TiagoJustino/surfcube/images/image00.jpg

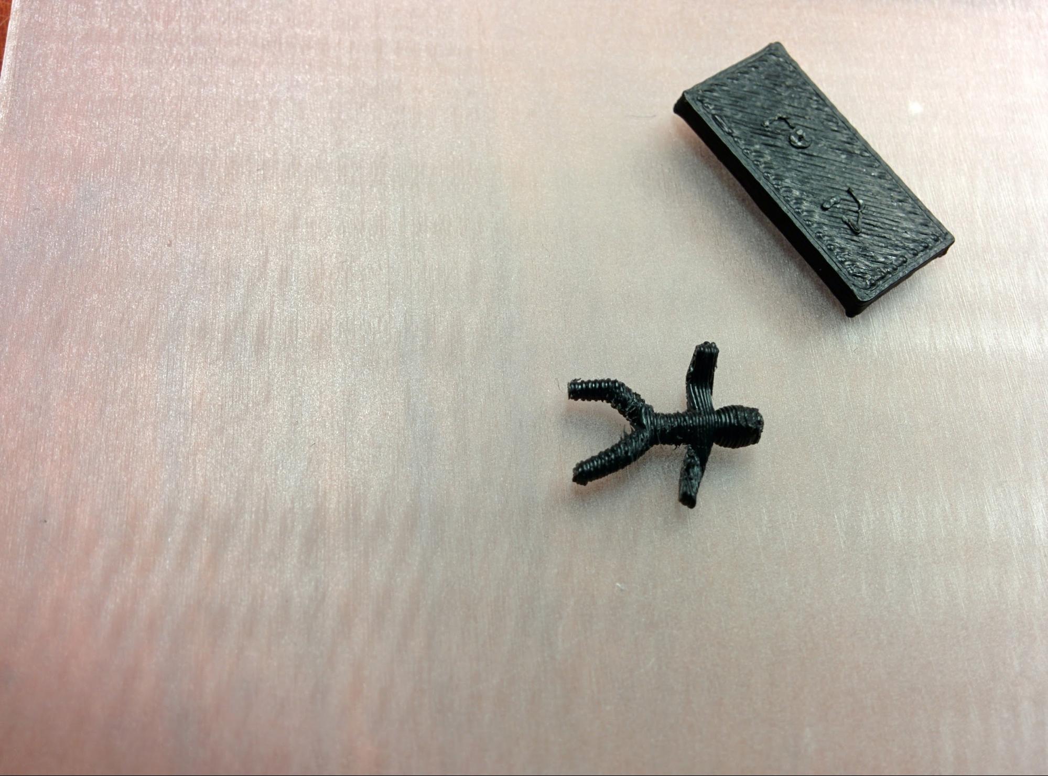
images/image00.jpg
