TiagoJustino/surfcube/sketches/IMG_20151026_231950.jpg

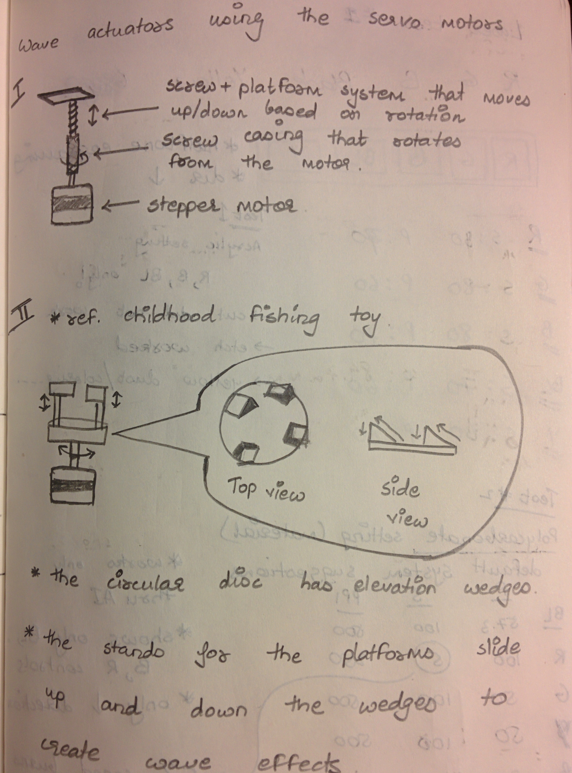
sketches/IMG_20151026_231950.jpg
