TiagoJustino/surfcube/sketches/IMG_20151026_232008.jpg

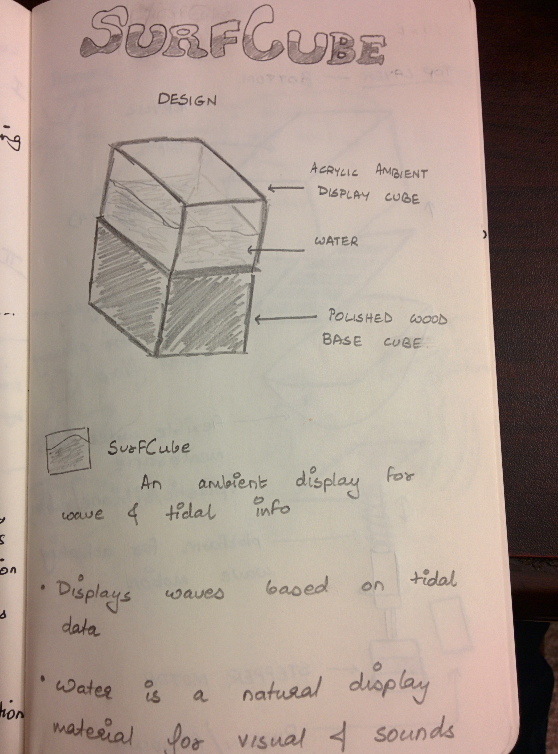
sketches/IMG_20151026_232008.jpg
