TiagoJustino/surfcube/sketches/IMG_20151026_232026.jpg

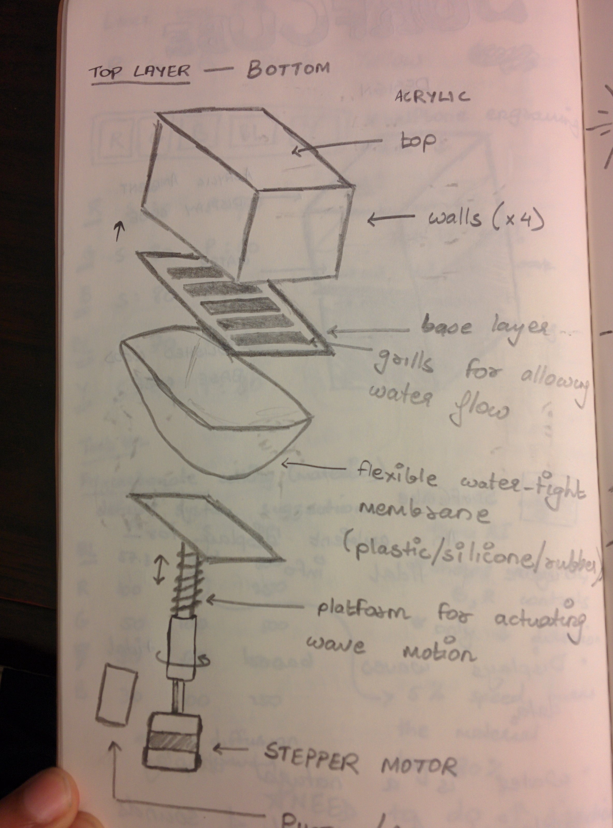
sketches/IMG_20151026_232026.jpg
