TiagoJustino/surfcube/sketches/IMG_20151026_232033.jpg

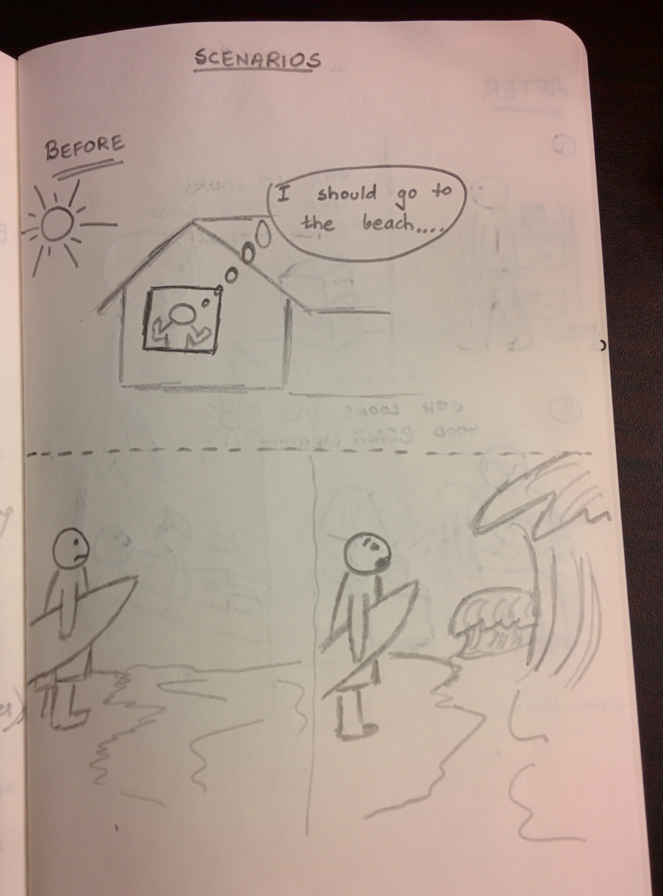
sketches/IMG_20151026_232033.jpg
