TiagoJustino/surfcube/sketches/IMG_20151026_232042.jpg

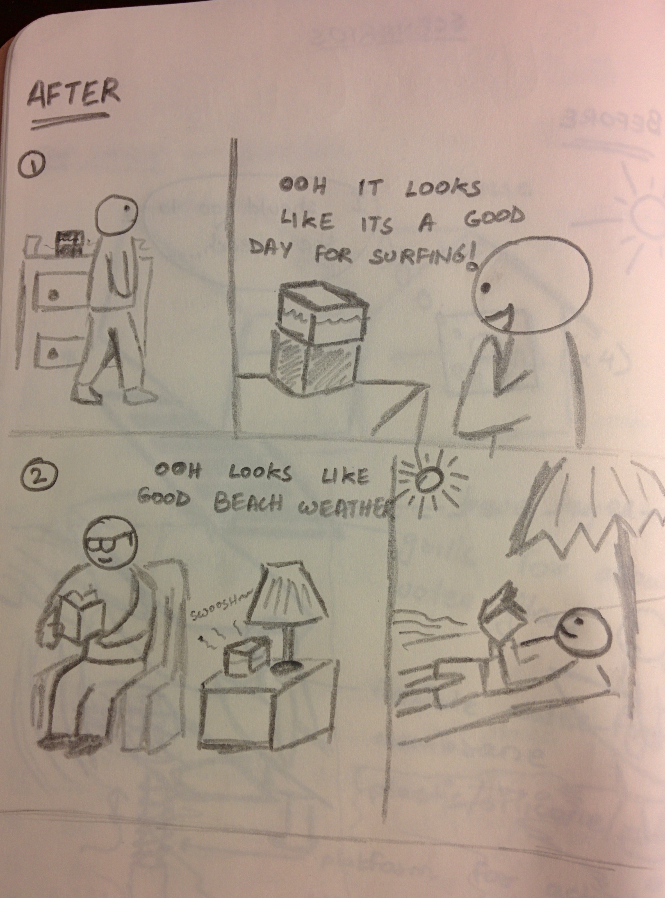
sketches/IMG_20151026_232042.jpg
